kacer/3D-Tracker-Vive/firmware/src/services.h

const static char* coordinatesServiceUUID              = "3d000000a000cafe040400451f003d3d";
const static char* coordinatesCharacteristicUUID       = "3d000000a001cafe040400451f003d3d";

const static char* baseStationGeometryServiceUUID      = "3d000000b000cafe040400451f003d3d";
const static char* stationNumberCharacteristicUUID     = "3d000000b001cafe040400451f003d3d";
const static char* positionCharacteristicUUID          = "3d000000b002cafe040400451f003d3d";
const static char* rotation1RowCharacteristicUUID      = "3d000000b003cafe040400451f003d3d";
const static char* rotation2RowCharacteristicUUID      = "3d000000b004cafe040400451f003d3d";
const static char* rotation3RowCharacteristicUUID      = "3d000000b005cafe040400451f003d3d";
